robertbullen/dakboard/docs/slides/design/apple-carplay.png

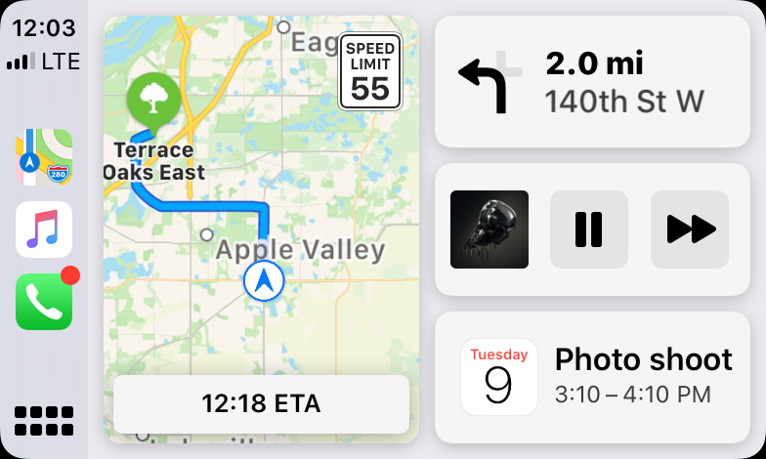
docs/slides/design/apple-carplay.png
