robertbullen/dakboard/docs/slides/design/dakboard-agenda-tan.jpg

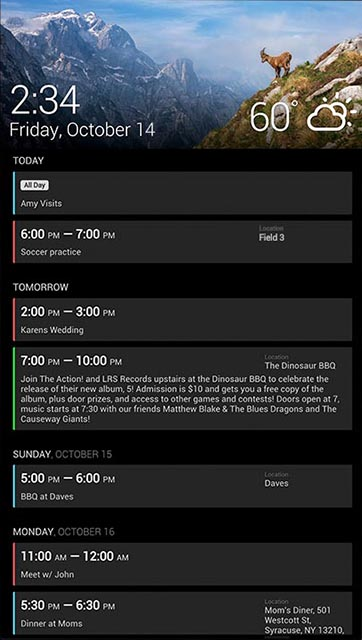
docs/slides/design/dakboard-agenda-tan.jpg
