robertbullen/dakboard/docs/slides/design/dakboard-big-calendar.png

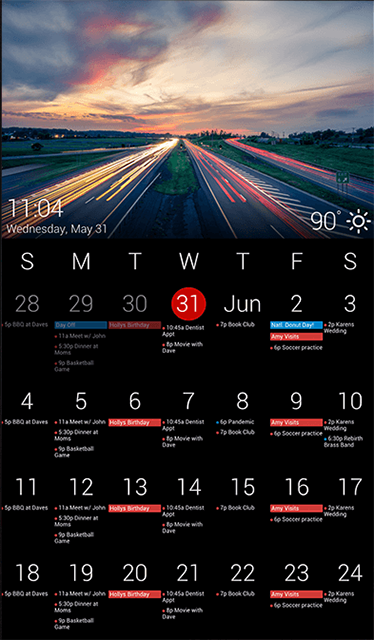
docs/slides/design/dakboard-big-calendar.png
