robertbullen/dakboard/docs/slides/design/dakboard-photo-frame.jpg

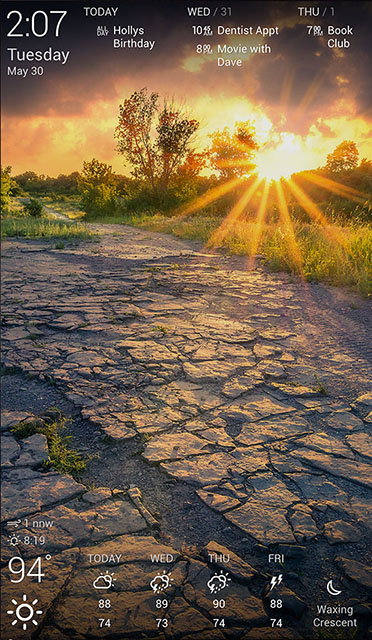
docs/slides/design/dakboard-photo-frame.jpg
