robertbullen/dakboard/docs/slides/design/dakboard-smarthome-dashboard.jpg

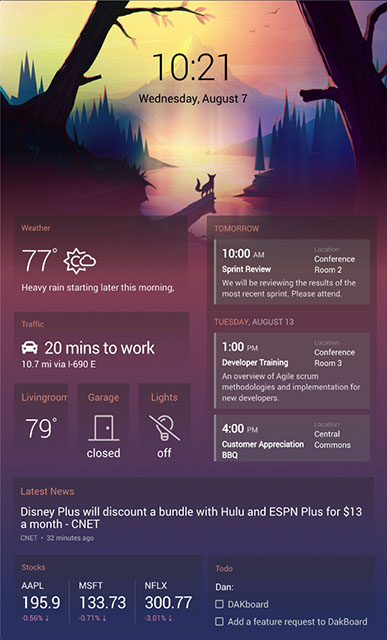
docs/slides/design/dakboard-smarthome-dashboard.jpg
