robertbullen/dakboard/docs/slides/hardware/raspberry-pi-4.jpg

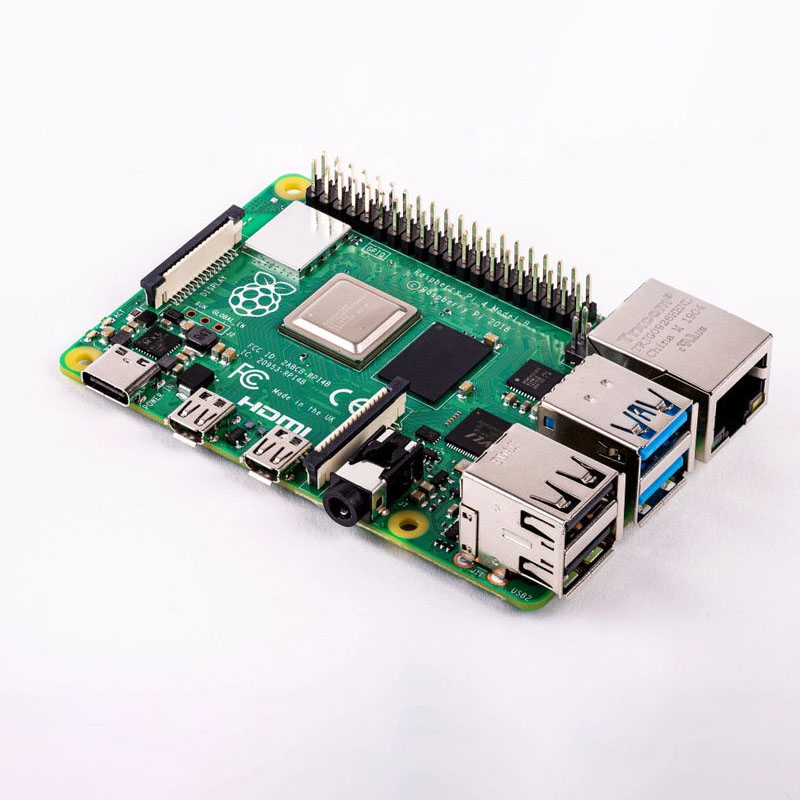
docs/slides/hardware/raspberry-pi-4.jpg
