robertbullen/dakboard/docs/slides/hardware/smraza-starter-kit.jpg

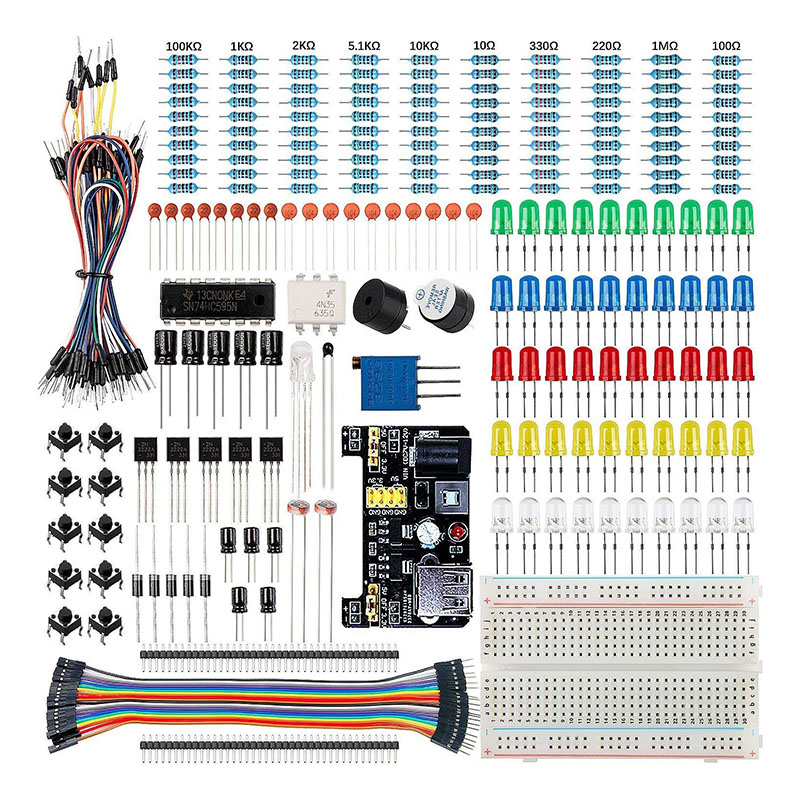
docs/slides/hardware/smraza-starter-kit.jpg
