robertbullen/dakboard/docs/slides/introduction/classroom-monthly-calendar.jpg

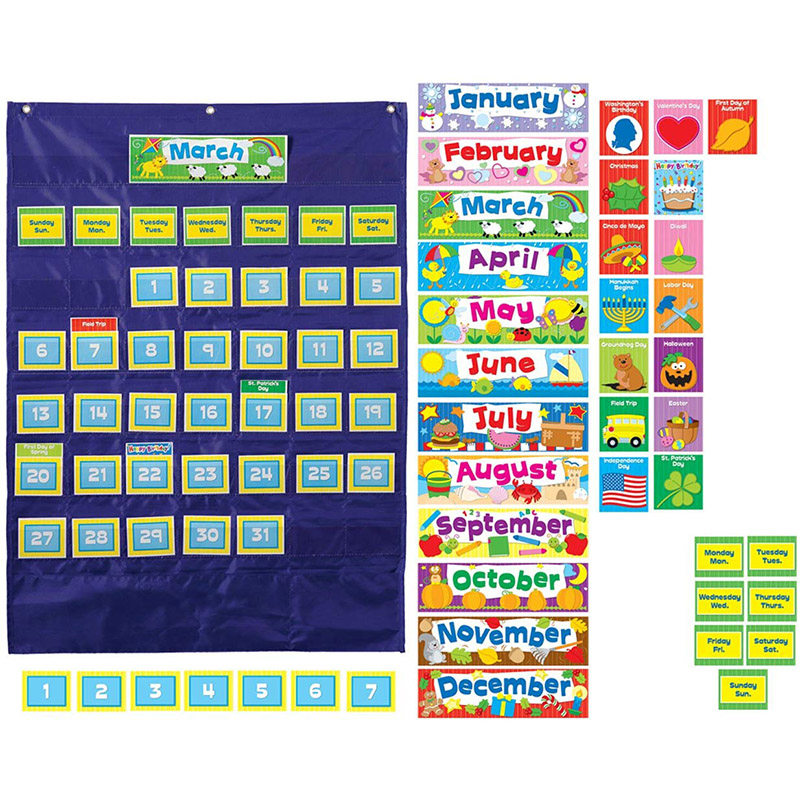
docs/slides/introduction/classroom-monthly-calendar.jpg
